directive0/TR-109/enclosure_design/STLs/Clear Diffuser Parts/TR109 - Diffuser - Sensor - Lower Right Strip.stl

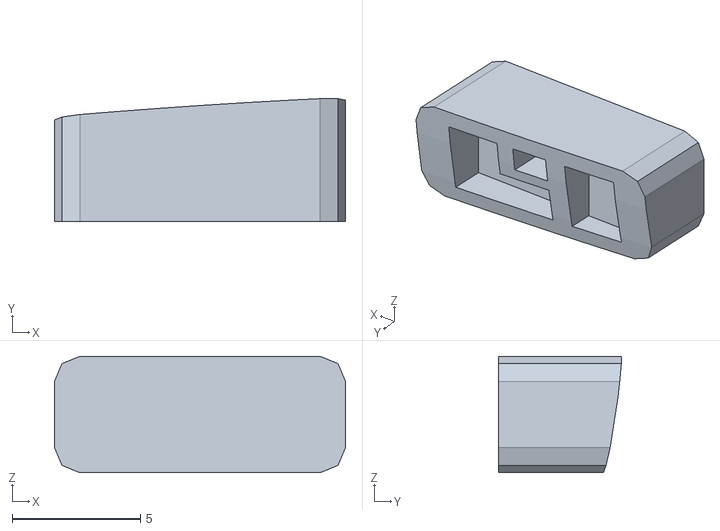
[picture p13: CAD file, 2025-04-25]
enclosure_design/STLs/Clear Diffuser Parts/TR109 - Diffuser - Sensor - Lower Right Strip.stl
11.4 x 4.79 x 4.54
