directive0/TR-109/enclosure_design/STLs/Shrouds/TR-109 Sensor Board Shrouds.stl

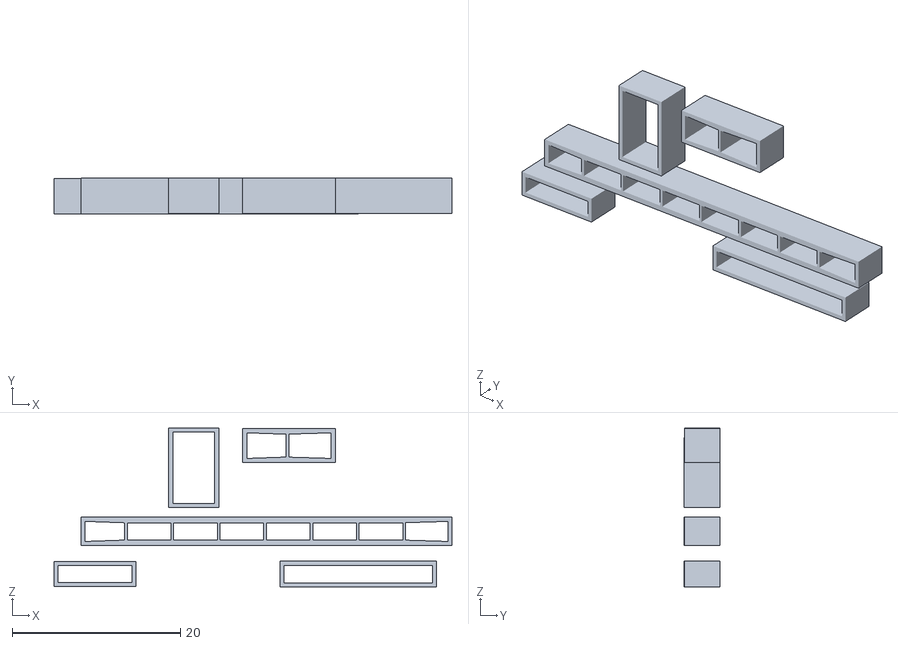
[picture p14: CAD file, 2025-06-26]
enclosure_design/STLs/Shrouds/TR-109 Sensor Board Shrouds.stl
47.3 x 4.27 x 18.9
