directive0/TR-109/enclosure_design/STLs/Spacers/TR109 - Spacer - GPIO Cut Guide.stl

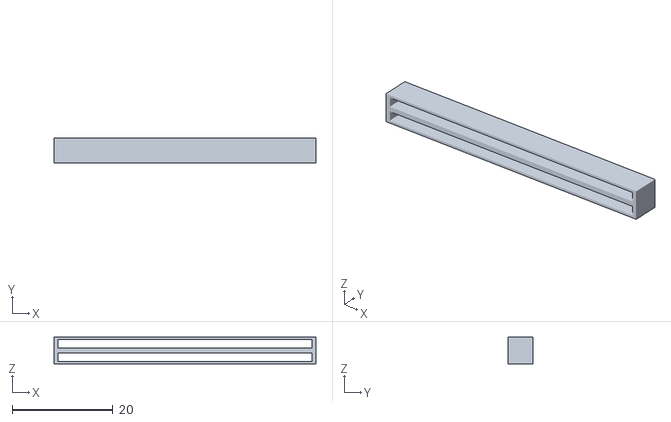
[picture p15: CAD file, 2025-06-26]
enclosure_design/STLs/Spacers/TR109 - Spacer - GPIO Cut Guide.stl
52.1 x 5.00 x 5.29
