directive0/TR-109/enclosure_design/STLs/TR109 - Door - EMRG Surround.stl

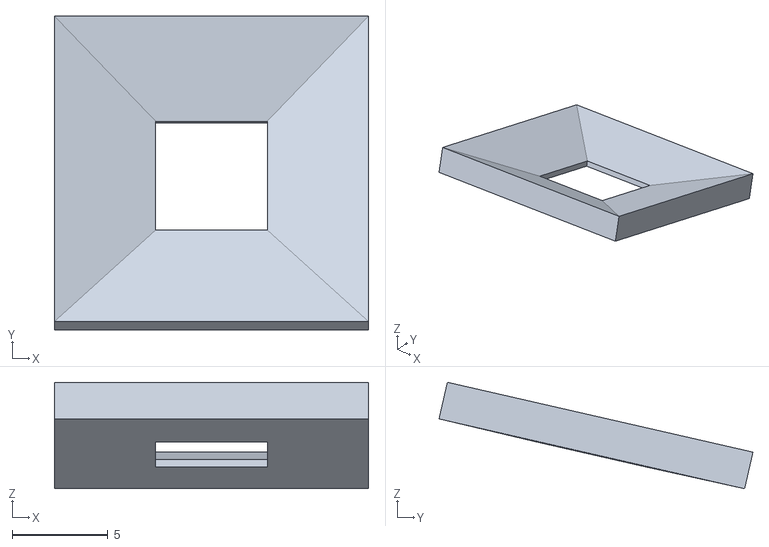
[picture p16: CAD file, 2025-06-26]
enclosure_design/STLs/TR109 - Door - EMRG Surround.stl
16.4 x 16.4 x 5.57
