directive0/TR-109/enclosure_design/STLs/Clear Diffuser Parts/TR109 - Diffuser - Sensor - 3mm LED Dummy.stl

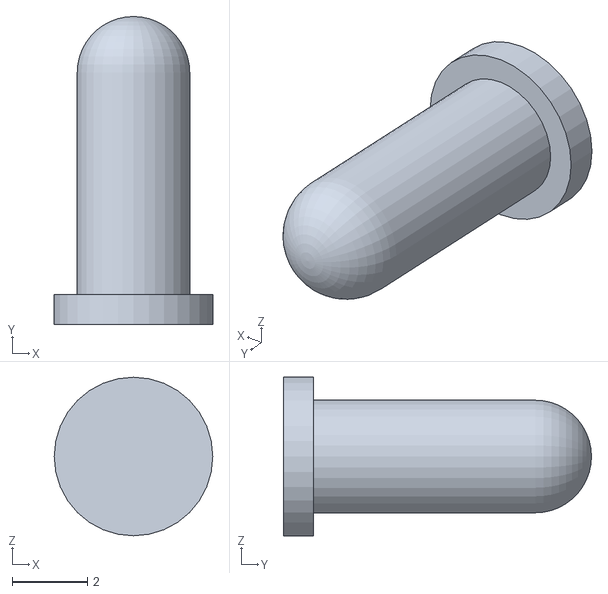
[picture p17: CAD file, 2025-04-25]
enclosure_design/STLs/Clear Diffuser Parts/TR109 - Diffuser - Sensor - 3mm LED Dummy.stl
4.23 x 8.21 x 4.23
