directive0/TR-109/enclosure_design/STLs/Spacers/TR109 - Spacer - 5.89mm pi spacer.stl

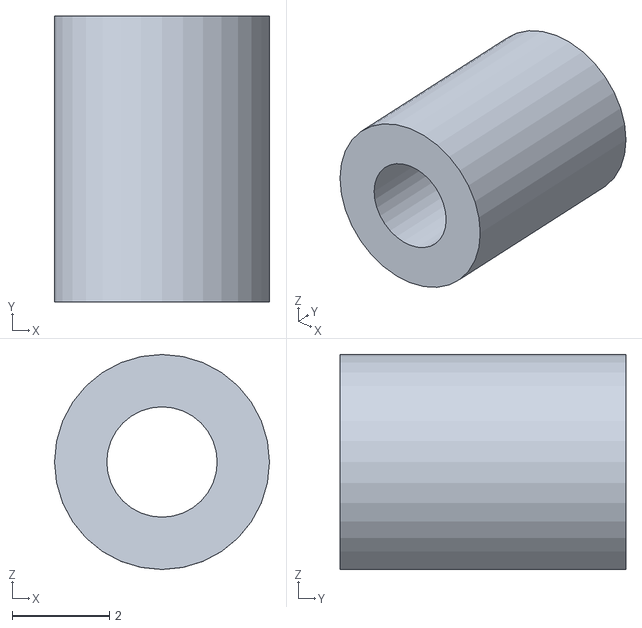
[picture p18: CAD file, 2025-04-25]
enclosure_design/STLs/Spacers/TR109 - Spacer - 5.89mm pi spacer.stl
4.43 x 5.89 x 4.43
