directive0/TR-109/enclosure_design/STLs/TR109 - Door - Hinge Outer.stl

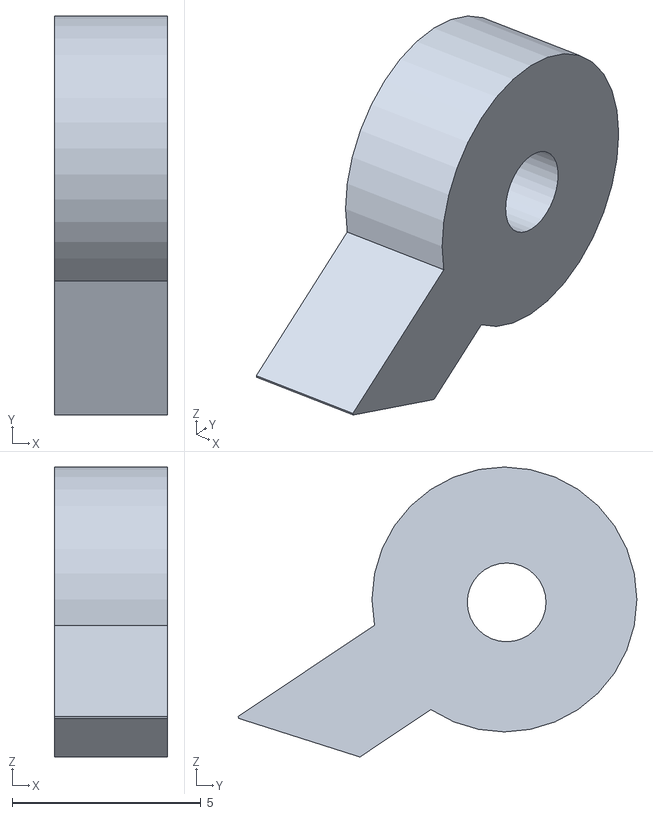
[picture p19: CAD file, 2025-04-25]
enclosure_design/STLs/TR109 - Door - Hinge Outer.stl
3.00 x 10.6 x 7.69
