directive0/TR-109/enclosure_design/STLs/Clear Diffuser Parts/TR109 - Diffuser - Sensor - Ripple.stl

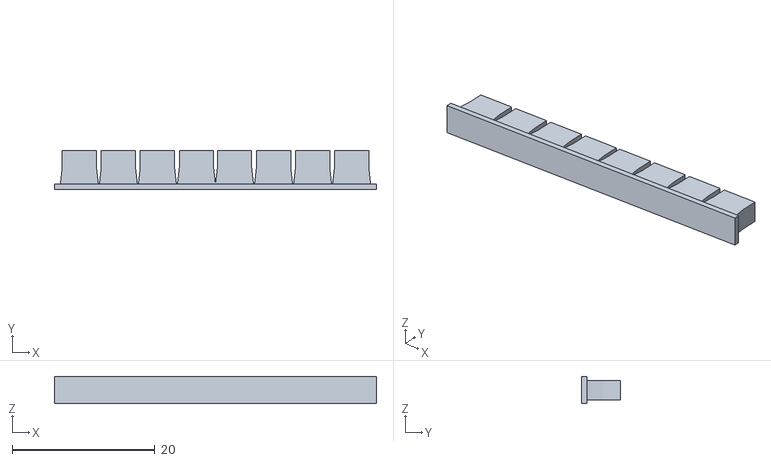
[picture p20: CAD file, 2025-04-25]
enclosure_design/STLs/Clear Diffuser Parts/TR109 - Diffuser - Sensor - Ripple.stl
45.1 x 5.41 x 3.84
