directive0/TR-109/enclosure_design/STLs/Spacers/TR109 - Spacer - 5mm pi spacer.stl

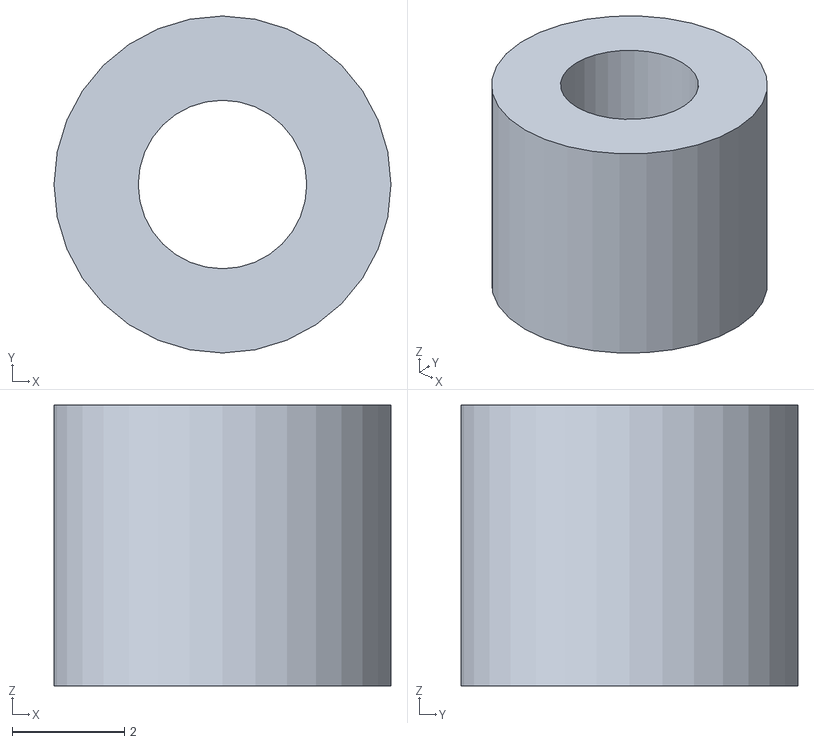
[picture p21: CAD file, 2025-04-25]
enclosure_design/STLs/Spacers/TR109 - Spacer - 5mm pi spacer.stl
6.00 x 6.00 x 5.00
