directive0/TR-109/enclosure_design/STLs/TR109 - Chassis.stl

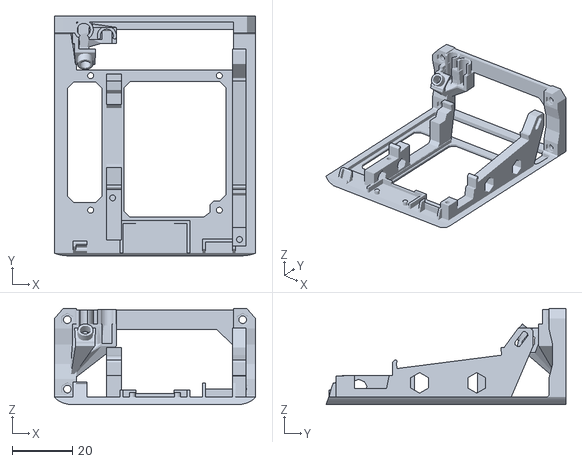
[picture p22: CAD file, 2025-04-25]
enclosure_design/STLs/TR109 - Chassis.stl
66.6 x 79.4 x 31.8
