directive0/TR-109/enclosure_design/STLs/Clear Diffuser Parts/TR109 - Diffuser - Sensor - Top Left Barrel.stl

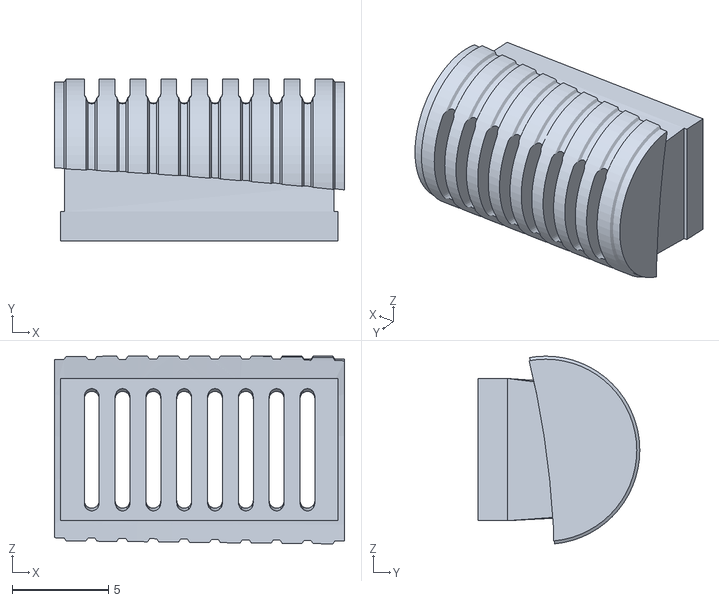
[picture p23: CAD file, 2025-04-25]
enclosure_design/STLs/Clear Diffuser Parts/TR109 - Diffuser - Sensor - Top Left Barrel.stl
15.1 x 8.40 x 9.76
