directive0/TR-109/enclosure_design/STLs/Spacers/TR109 - Spacer - ABDG Lights.stl

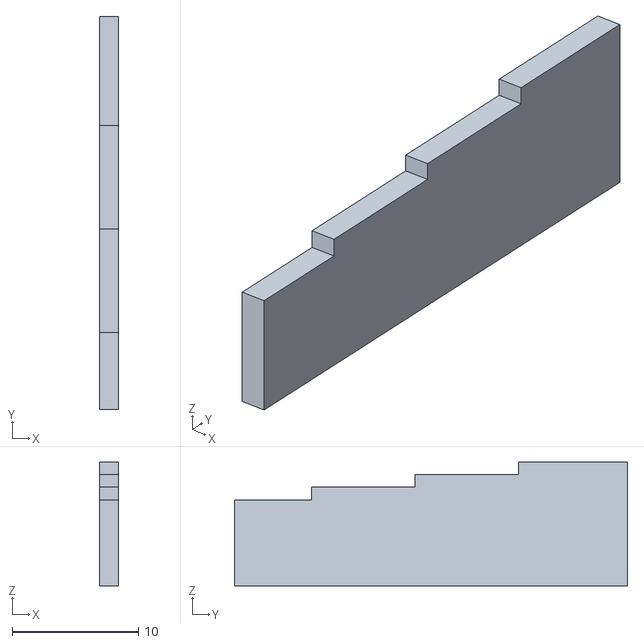
[picture p24: CAD file, 2021-07-17]
enclosure_design/STLs/Spacers/TR109 - Spacer - ABDG Lights.stl
1.50 x 31.2 x 9.84
