directive0/TR-109/enclosure_design/STLs/TR109 - Pi and Chassis Spacer (.6mm).stl

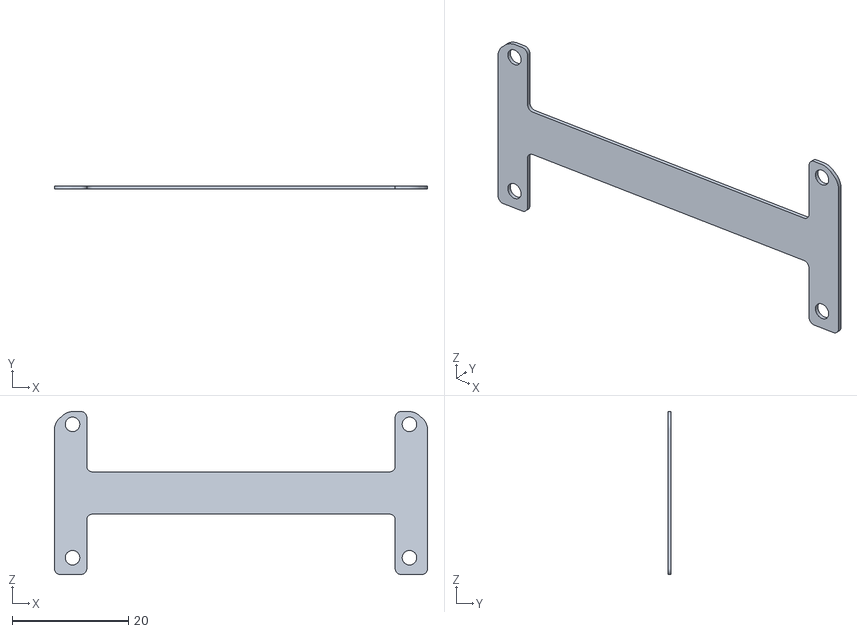
[picture p25: CAD file, 2025-04-25]
enclosure_design/STLs/TR109 - Pi and Chassis Spacer (.6mm).stl
64.2 x 0.6 x 28.1
