directive0/TR-109/enclosure_design/STLs/Clear Diffuser Parts/TR109 - Diffuser - Door - EMRG.stl

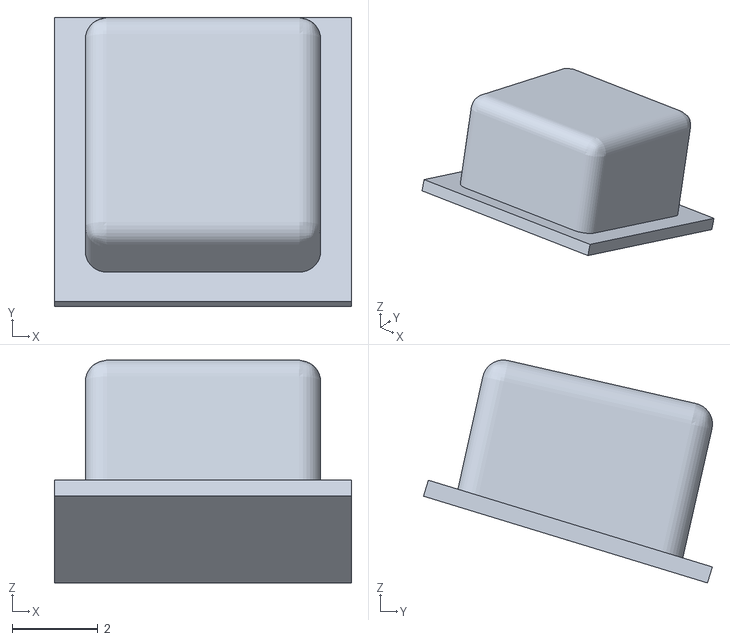
[picture p26: CAD file, 2025-04-25]
enclosure_design/STLs/Clear Diffuser Parts/TR109 - Diffuser - Door - EMRG.stl
6.94 x 6.75 x 5.21
