directive0/TR-109/enclosure_design/STLs/TR109 - Door - Mk 3 Hingeless.stl

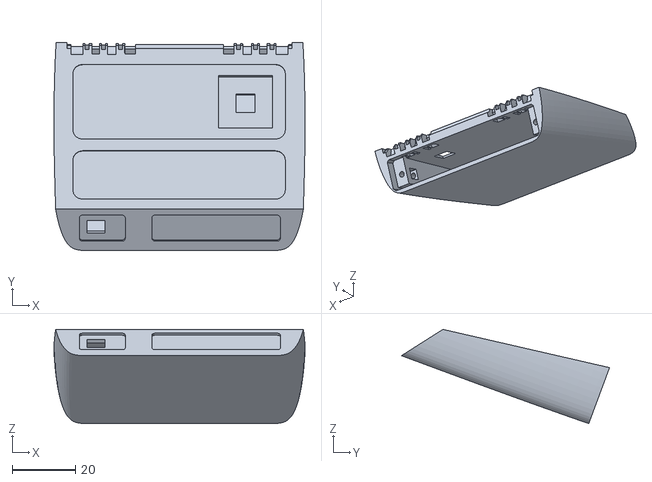
[picture p27: CAD file, 2025-04-25]
enclosure_design/STLs/TR109 - Door - Mk 3 Hingeless.stl
79.2 x 65.6 x 29.7
