directive0/TR-109/enclosure_design/STLs/Clear Diffuser Parts/TR109 - Diffuser - Sensor - Lower Left Strip.stl

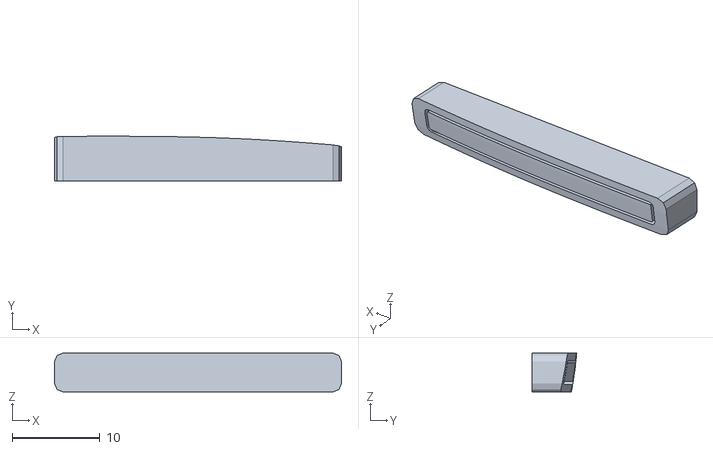
[picture p29: CAD file, 2025-04-25]
enclosure_design/STLs/Clear Diffuser Parts/TR109 - Diffuser - Sensor - Lower Left Strip.stl
32.8 x 5.09 x 4.45
