directive0/TR-109/enclosure_design/STLs/TR109 - Door - Hinge  Inner.stl

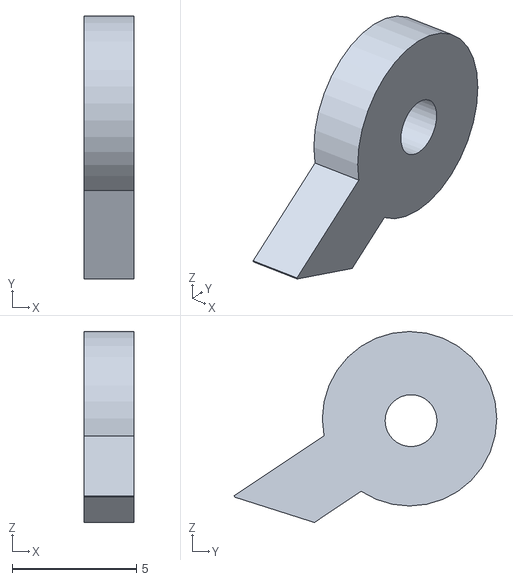
[picture p30: CAD file, 2025-04-25]
enclosure_design/STLs/TR109 - Door - Hinge Inner.stl
2.00 x 10.6 x 7.69
