directive0/TR-109/enclosure_design/STLs/TR109 - Sensor Plate - White Surround.stl

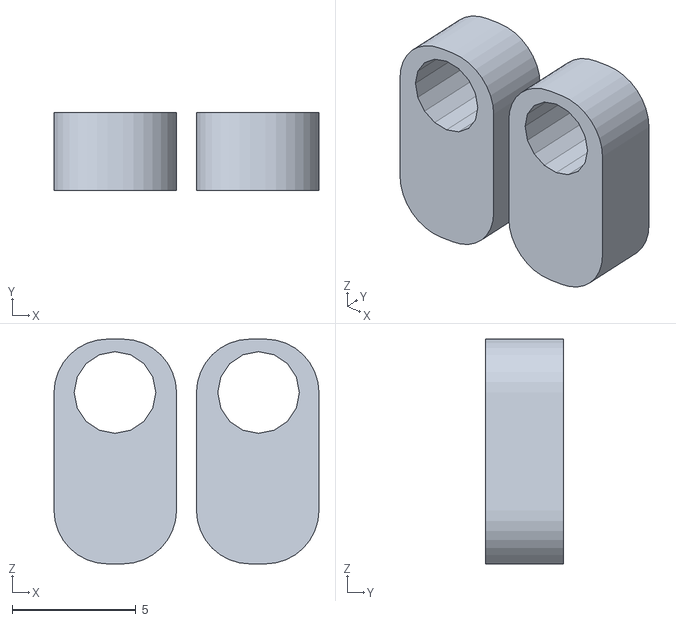
[picture p31: CAD file, 2025-04-25]
enclosure_design/STLs/TR109 - Sensor Plate - White Surround.stl
10.7 x 3.15 x 9.08
