directive0/TR-109/enclosure_design/STLs/TR109 - Door.stl

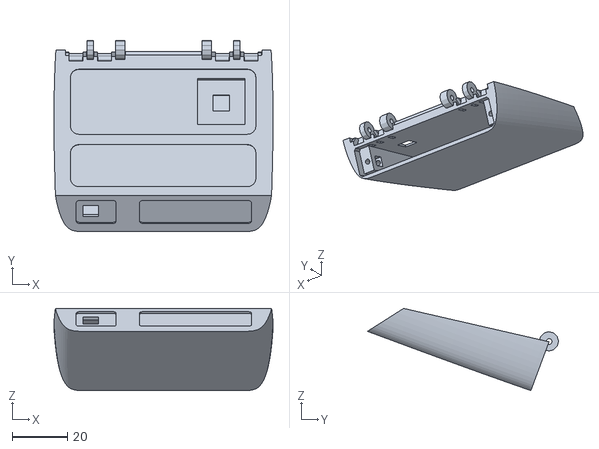
[picture p32: CAD file, 2025-04-25]
enclosure_design/STLs/TR109 - Door.stl
79.2 x 69.1 x 29.7
