directive0/TR-109/enclosure_design/STLs/TR109 - Sensor Plate.stl

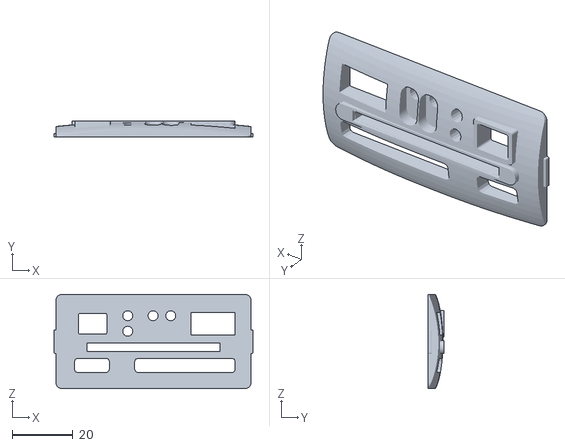
[picture p33: CAD file, 2025-04-25]
enclosure_design/STLs/TR109 - Sensor Plate.stl
65.4 x 5.38 x 30.9
