directive0/TR-109/enclosure_design/STLs/TR109 - Capacitive Button Pads.stl

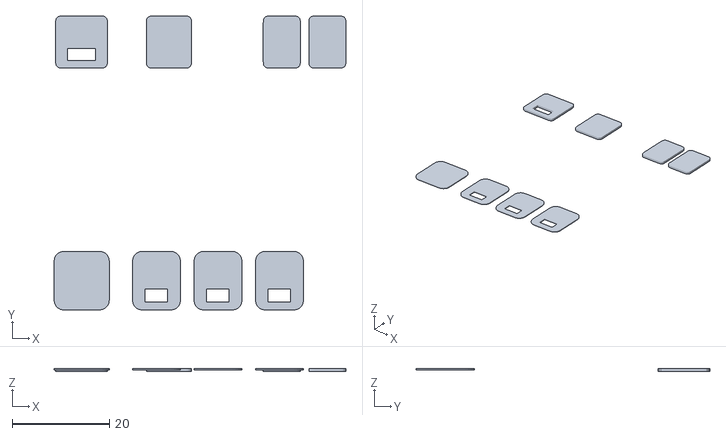
[picture p34: CAD file, 2025-04-25]
enclosure_design/STLs/TR109 - Capacitive Button Pads.stl
60.0 x 60.4 x 0.687
