directive0/TR-109/enclosure_design/STLs/TR109 - Door Chassis.stl

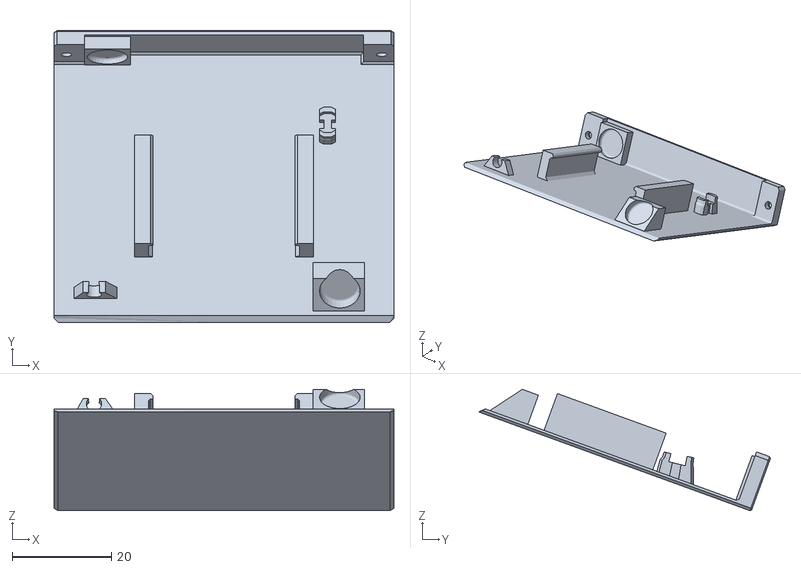
[picture p35: CAD file, 2025-04-25]
enclosure_design/STLs/TR109 - Door Chassis.stl
68.5 x 58.8 x 24.5
