directive0/TR-109/enclosure_design/STLs/TR109 - End Cap.stl

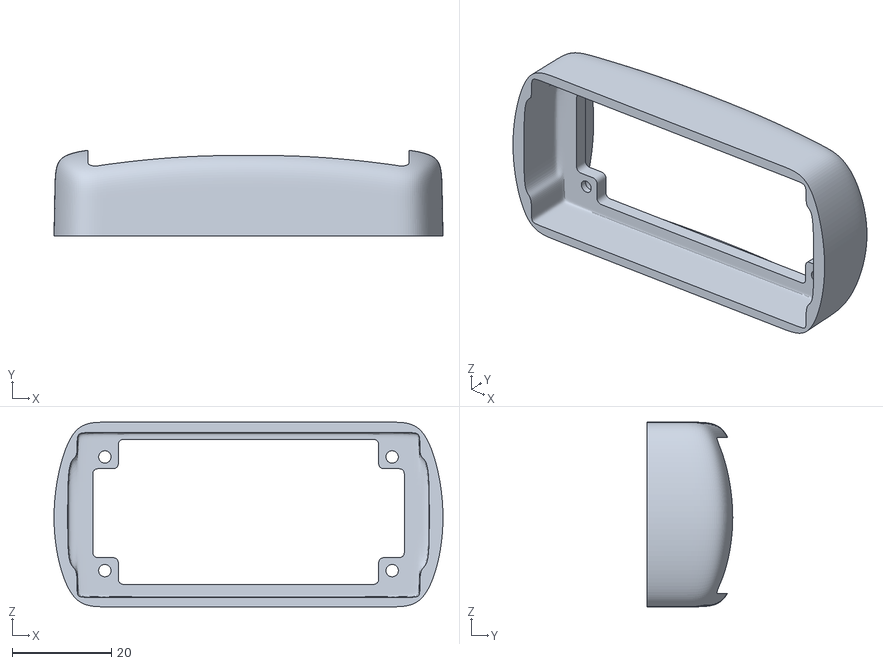
[picture p36: CAD file, 2021-08-13]
enclosure_design/STLs/TR109 - End Cap.stl
78.6 x 17.3 x 37.3
