directive0/TR-109/enclosure_design/STLs/tr-109 picorder shell-Mark_2_Door.stl

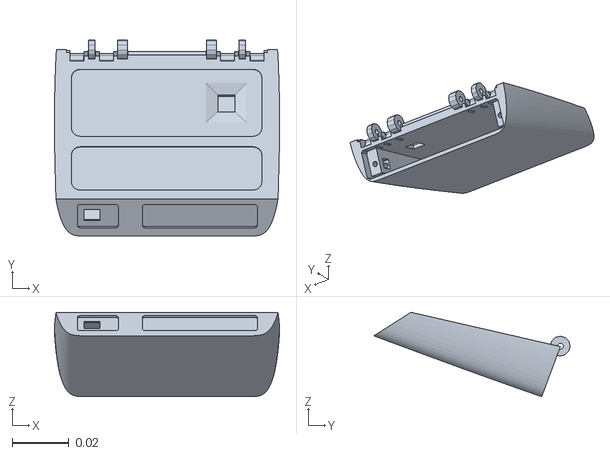
[picture p37: CAD file, 2021-06-29]
enclosure_design/STLs/tr-109 picorder shell-Mark_2_Door.stl
0.0792 x 0.0691 x 0.0297
